3dPaulHarvey/Cycloidal-Robot-Wrist-3DOF-C.L.A.W.1-/SolidWorks/3D3-F-J6- Cycloidal A 56 5 1.5 14-1.SLDPRT

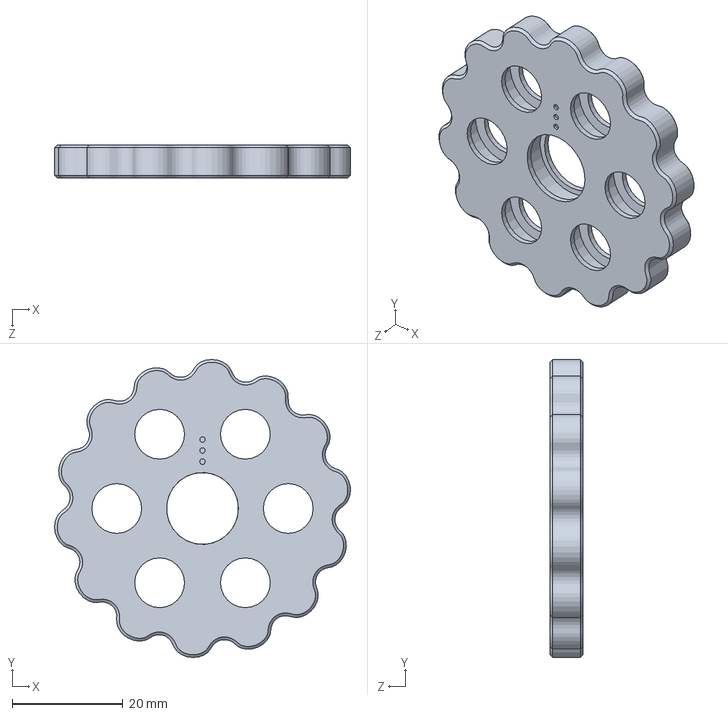
[picture p18: CAD file, 2022-01-06]
SolidWorks/3D3-F-J6- Cycloidal A 56 5 1.5 14-1.SLDPRT
53.5 x 53.9 x 6.00 mm
