3dPaulHarvey/Cycloidal-Robot-Wrist-3DOF-C.L.A.W.1-/SolidWorks/3D3- J6-3- 3MM PIN.SLDPRT

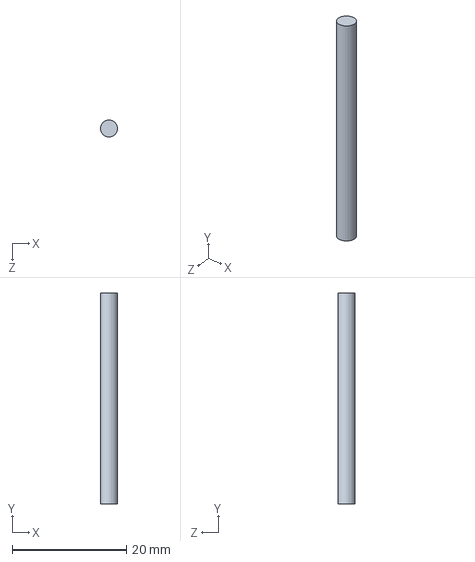
[picture p19: CAD file, 2022-01-06]
SolidWorks/3D3- J6-3- 3MM PIN.SLDPRT
3.00 x 37.0 x 3.00 mm
