3dPaulHarvey/Cycloidal-Robot-Wrist-3DOF-C.L.A.W.1-/SolidWorks/BEARING- 5x10x4.SLDPRT

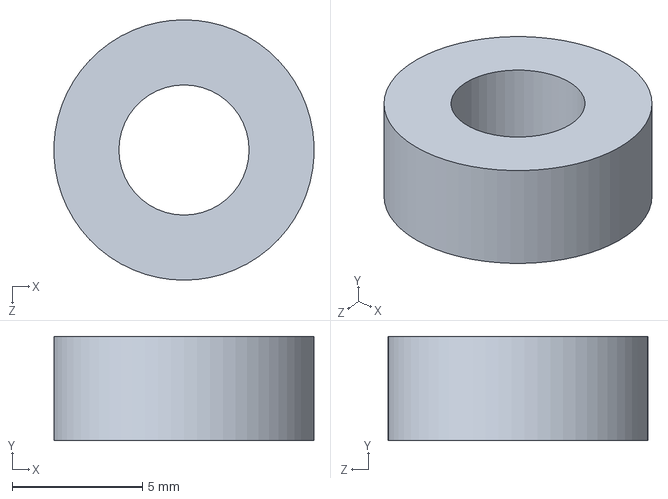
[picture p20: CAD file, 2022-01-06]
SolidWorks/BEARING- 5x10x4.SLDPRT
9.99 x 4.00 x 10.0 mm
