3dPaulHarvey/Cycloidal-Robot-Wrist-3DOF-C.L.A.W.1-/SolidWorks/3D3- J4 ECCENTRIC SHAFT.SLDPRT

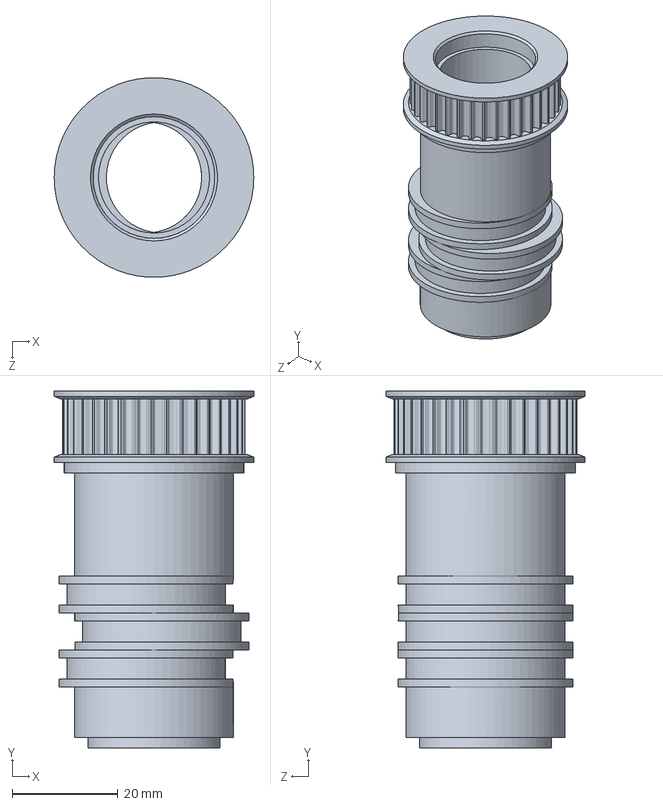
[picture p21: CAD file, 2022-01-06]
SolidWorks/3D3- J4 ECCENTRIC SHAFT.SLDPRT
37.7 x 67.5 x 37.7 mm
