3dPaulHarvey/Cycloidal-Robot-Wrist-3DOF-C.L.A.W.1-/SolidWorks/3D3-F-J5- 3MM PINS.SLDPRT

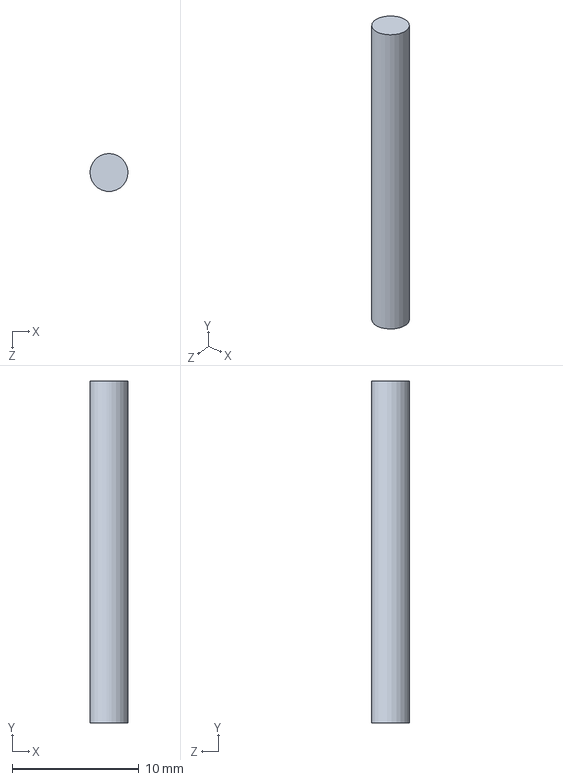
[picture p22: CAD file, 2022-01-06]
SolidWorks/3D3-F-J5- 3MM PINS.SLDPRT
2.99 x 27.0 x 3.00 mm
