3dPaulHarvey/Cycloidal-Robot-Wrist-3DOF-C.L.A.W.1-/SolidWorks/Cycloidal Lobes 19-1, 70, 5, 1.5- B.SLDPRT

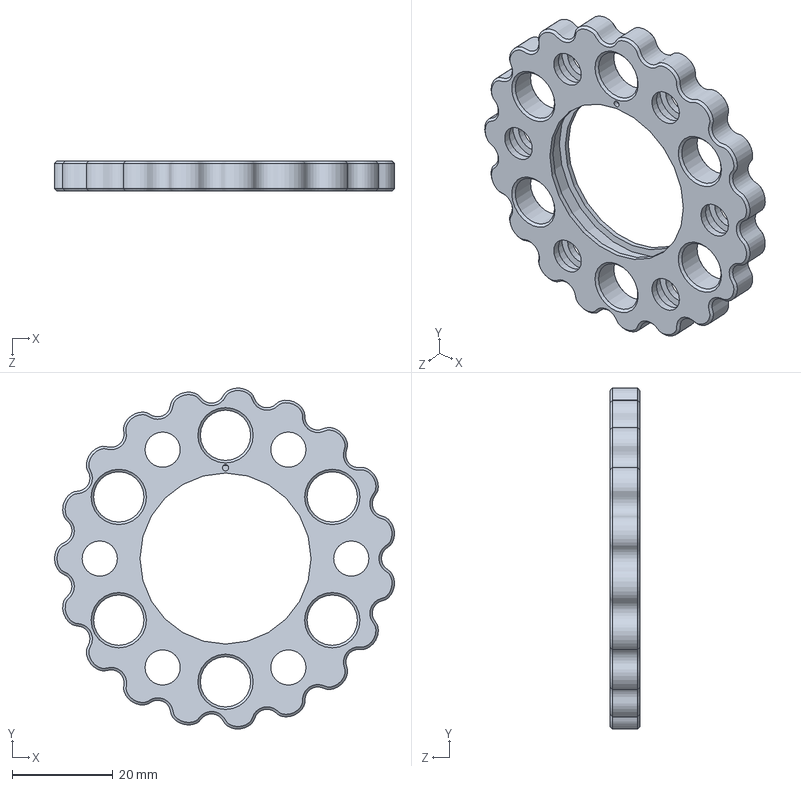
[picture p23: CAD file, 2022-01-06]
SolidWorks/Cycloidal Lobes 19-1, 70, 5, 1.5- B.SLDPRT
67.6 x 67.8 x 6.00 mm
