3dPaulHarvey/Cycloidal-Robot-Wrist-3DOF-C.L.A.W.1-/SolidWorks/BEARING- 3x5x5.SLDPRT

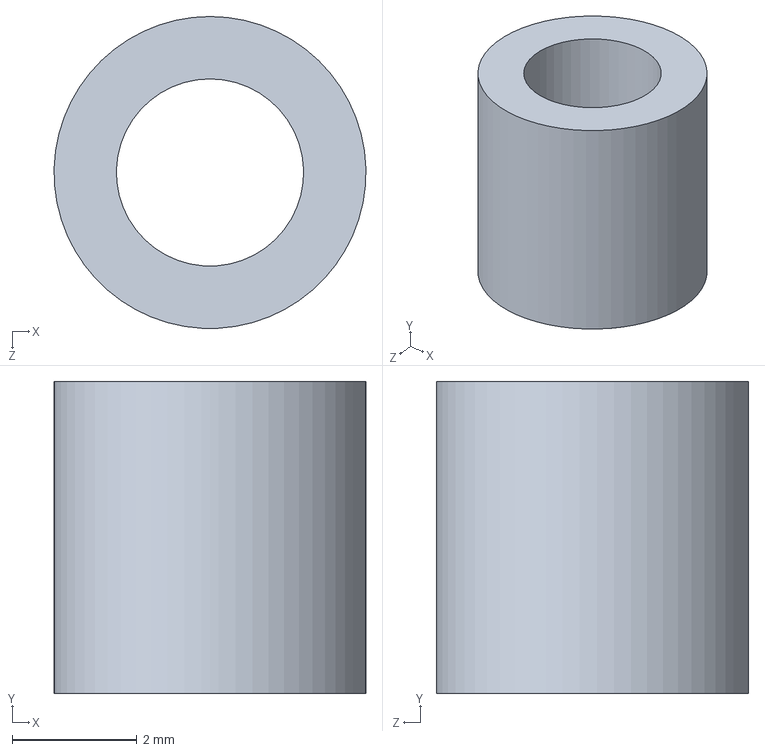
[picture p24: CAD file, 2022-01-06]
SolidWorks/BEARING- 3x5x5.SLDPRT
5.00 x 5.00 x 5.00 mm
