3dPaulHarvey/Cycloidal-Robot-Wrist-3DOF-C.L.A.W.1-/SolidWorks/3D3- J4- OUTPUT CARRIAGE.SLDPRT

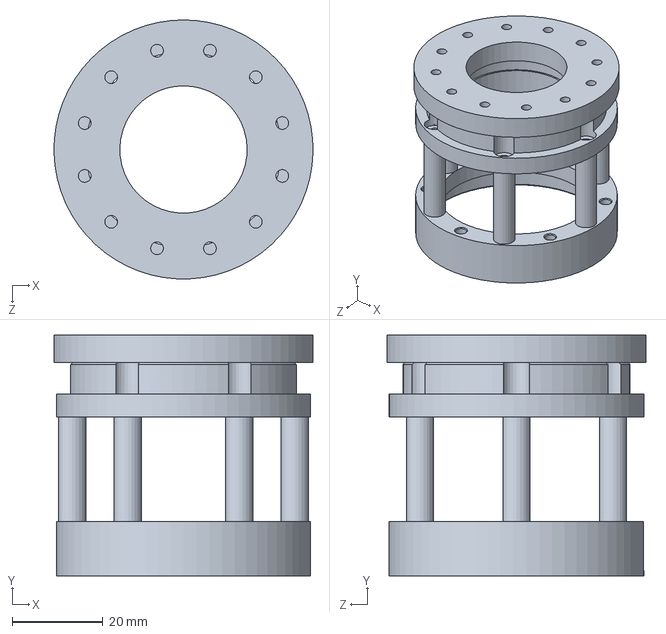
[picture p25: CAD file, 2022-01-06]
SolidWorks/3D3- J4- OUTPUT CARRIAGE.SLDPRT
57.0 x 53.0 x 57.0 mm
