3dPaulHarvey/Cycloidal-Robot-Wrist-3DOF-C.L.A.W.1-/SolidWorks/3D3- J5-2- MID WRIST FRAME.SLDPRT

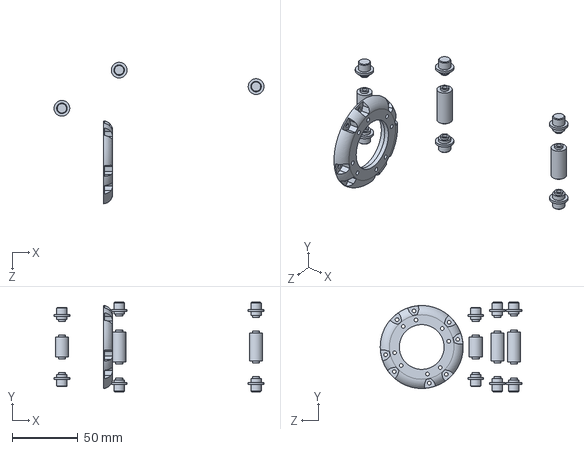
[picture p26: CAD file, 2022-01-06]
SolidWorks/3D3- J5-2- MID WRIST FRAME.SLDPRT
159.5 x 68.0 x 107.5 mm
