3dPaulHarvey/Cycloidal-Robot-Wrist-3DOF-C.L.A.W.1-/SolidWorks/3D3-J5-2- CYCLOIDAL 11-1rat 48dia 5dia 1.5ecc A.SLDPRT

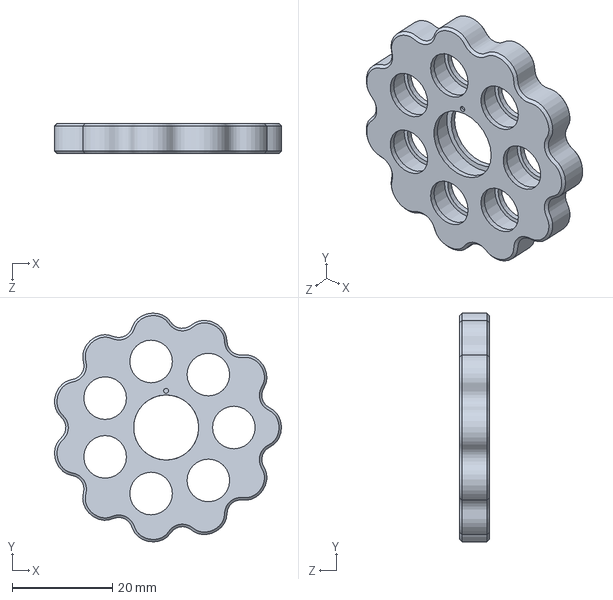
[picture p27: CAD file, 2022-01-06]
SolidWorks/3D3-J5-2- CYCLOIDAL 11-1rat 48dia 5dia 1.5ecc A.SLDPRT
45.3 x 45.6 x 6.00 mm
