3dPaulHarvey/Cycloidal-Robot-Wrist-3DOF-C.L.A.W.1-/SolidWorks/3D3-F-J5- DUMMY PINS.SLDPRT

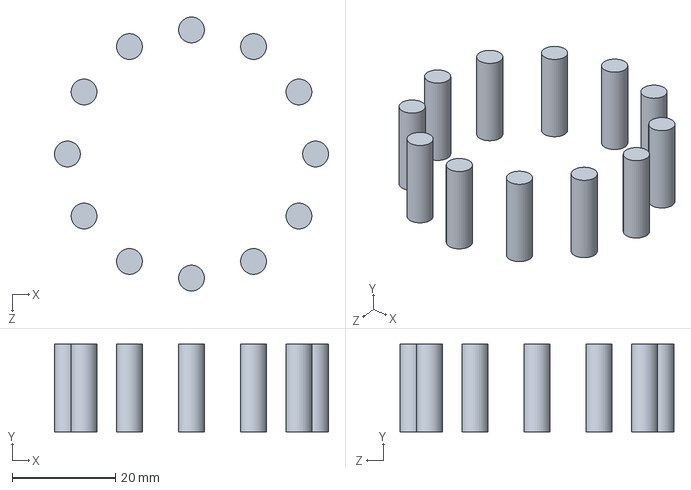
[picture p28: CAD file, 2022-01-06]
SolidWorks/3D3-F-J5- DUMMY PINS.SLDPRT
53.0 x 17.0 x 53.0 mm
