3dPaulHarvey/Cycloidal-Robot-Wrist-3DOF-C.L.A.W.1-/SolidWorks/3D3- J4- OUTER HOUSING.SLDPRT

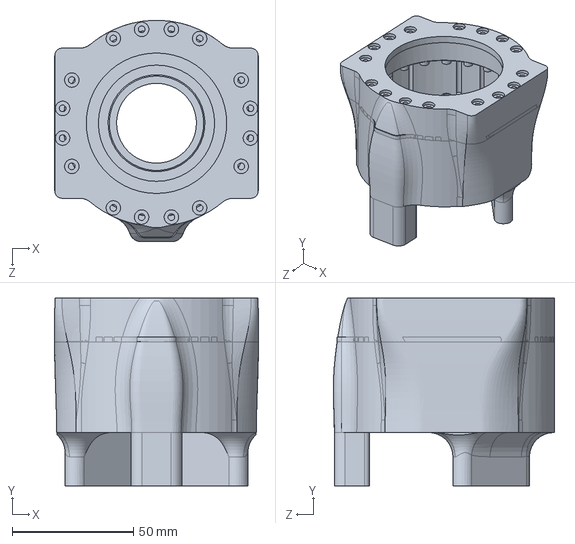
[picture p29: CAD file, 2022-01-06]
SolidWorks/3D3- J4- OUTER HOUSING.SLDPRT
84.2 x 77.5 x 91.4 mm
