3dPaulHarvey/Cycloidal-Robot-Wrist-3DOF-C.L.A.W.1-/SolidWorks/3D3- OUTER SHAFT.SLDPRT

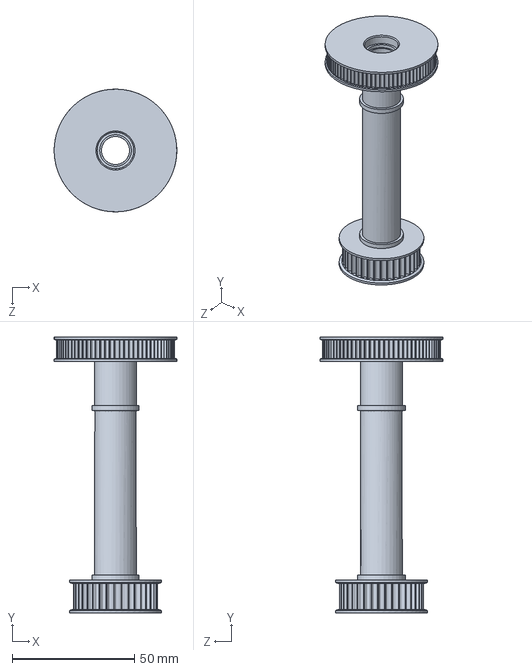
[picture p30: CAD file, 2022-01-06]
SolidWorks/3D3- OUTER SHAFT.SLDPRT
50.2 x 113.0 x 50.2 mm
