3dPaulHarvey/Cycloidal-Robot-Wrist-3DOF-C.L.A.W.1-/SolidWorks/3D3-F-J5- 3MM CORNER BAR B.SLDPRT

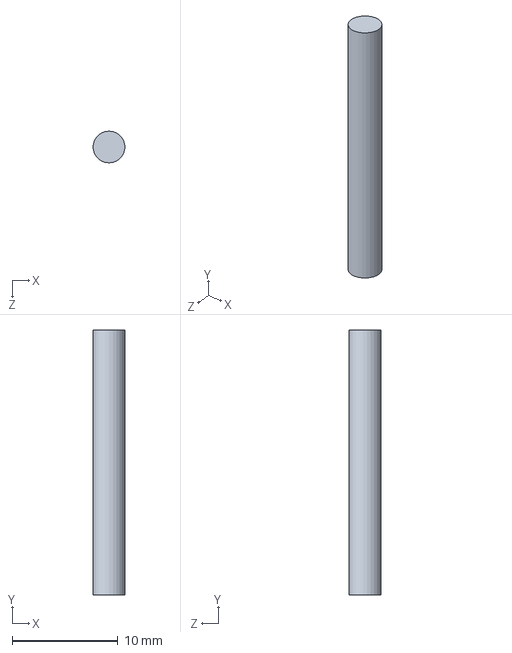
[picture p31: CAD file, 2022-01-06]
SolidWorks/3D3-F-J5- 3MM CORNER BAR B.SLDPRT
2.98 x 25.0 x 3.00 mm
