3dPaulHarvey/Cycloidal-Robot-Wrist-3DOF-C.L.A.W.1-/SolidWorks/gt2 35.SLDPRT

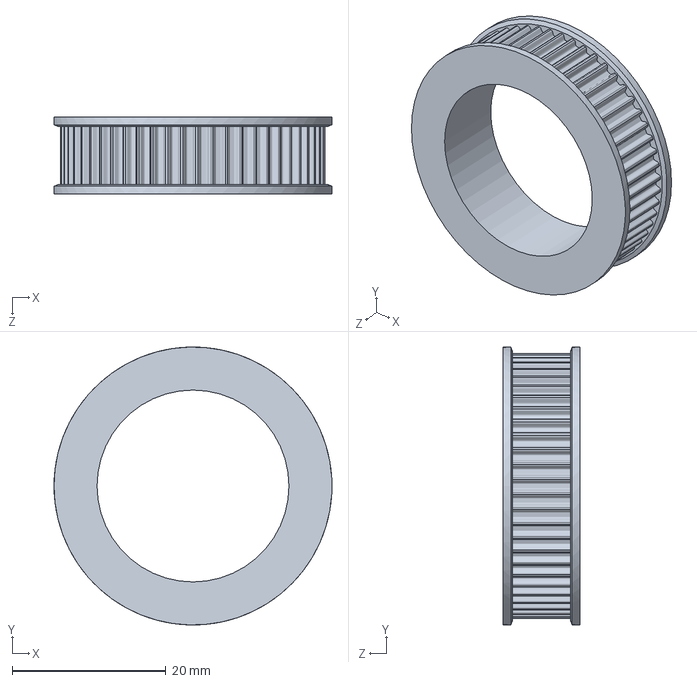
[picture p32: CAD file, 2022-01-02]
SolidWorks/gt2 35.SLDPRT
36.2 x 36.2 x 10.0 mm
