3dPaulHarvey/Cycloidal-Robot-Wrist-3DOF-C.L.A.W.1-/SolidWorks/44.SLDPRT

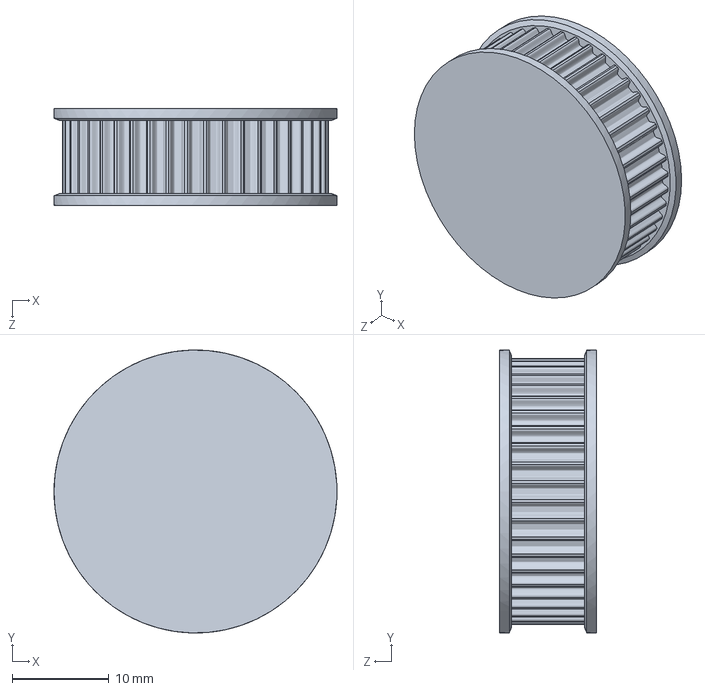
[picture p33: CAD file, 2022-01-02]
SolidWorks/44.SLDPRT
29.2 x 29.2 x 10.0 mm
