3dPaulHarvey/Cycloidal-Robot-Wrist-3DOF-C.L.A.W.1-/SolidWorks/3D3- J6-3- CORNER PULLEY.SLDPRT

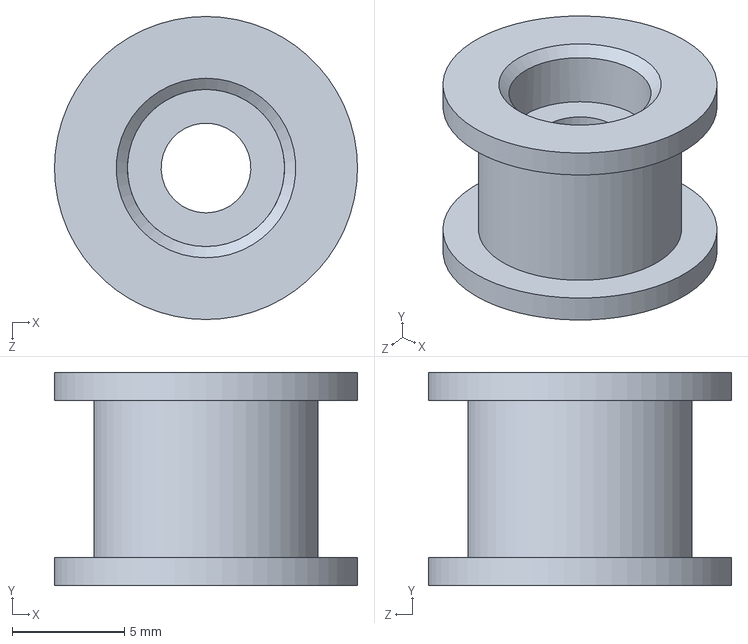
[picture p34: CAD file, 2022-01-02]
SolidWorks/3D3- J6-3- CORNER PULLEY.SLDPRT
13.5 x 9.50 x 13.5 mm
