3dPaulHarvey/Cycloidal-Robot-Wrist-3DOF-C.L.A.W.1-/SolidWorks/3D3- J6-3- 3MM BAR.SLDPRT

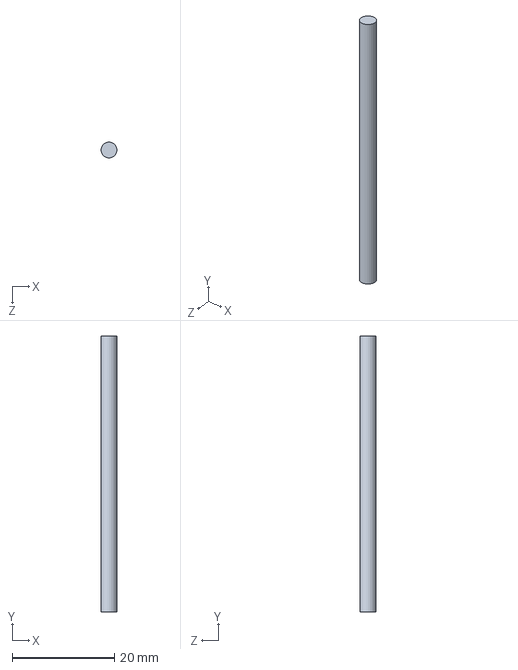
[picture p35: CAD file, 2022-01-02]
SolidWorks/3D3- J6-3- 3MM BAR.SLDPRT
3.10 x 54.0 x 3.10 mm
