3dPaulHarvey/Cycloidal-Robot-Wrist-3DOF-C.L.A.W.1-/SolidWorks/3D3- LEFT DRIVE PULLEY.SLDPRT

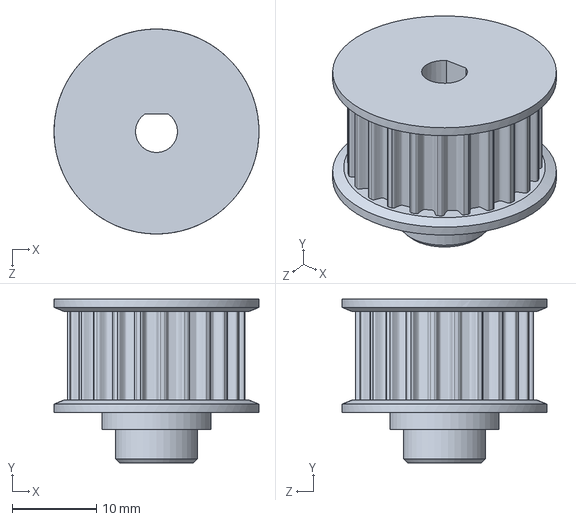
[picture p36: CAD file, 2022-01-02]
SolidWorks/3D3- LEFT DRIVE PULLEY.SLDPRT
24.4 x 19.5 x 24.4 mm
