3dPaulHarvey/Cycloidal-Robot-Wrist-3DOF-C.L.A.W.1-/SolidWorks/GT2-60T-ID 35.2-PD 38.2.SLDPRT

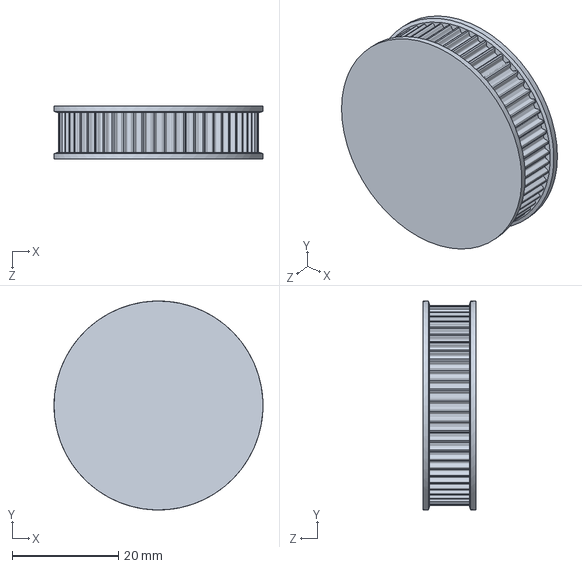
[picture p37: CAD file, 2022-01-02]
SolidWorks/GT2-60T-ID 35.2-PD 38.2.SLDPRT
39.4 x 39.4 x 10.0 mm
