3dPaulHarvey/Cycloidal-Robot-Wrist-3DOF-C.L.A.W.1-/SolidWorks/GT2-65T-ID 38.4-PD 41.4.SLDPRT

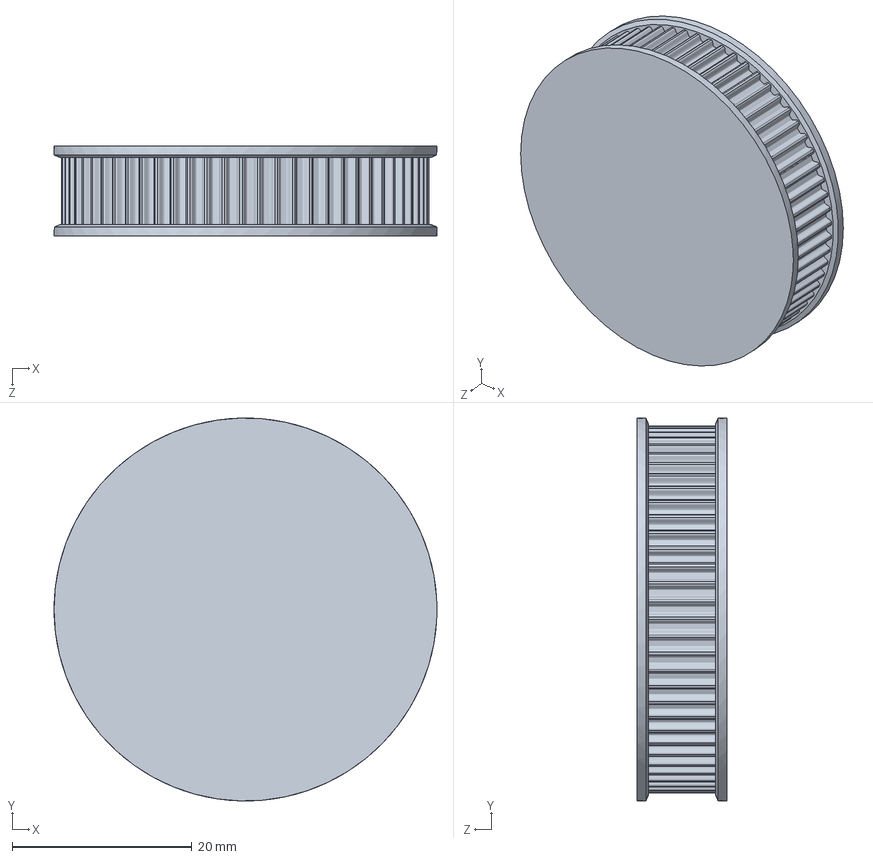
[picture p38: CAD file, 2022-01-02]
SolidWorks/GT2-65T-ID 38.4-PD 41.4.SLDPRT
42.6 x 42.6 x 10.0 mm
