3dPaulHarvey/Cycloidal-Robot-Wrist-3DOF-C.L.A.W.1-/SolidWorks/GT2-50T-ID 28.9-PD 31.85.SLDPRT

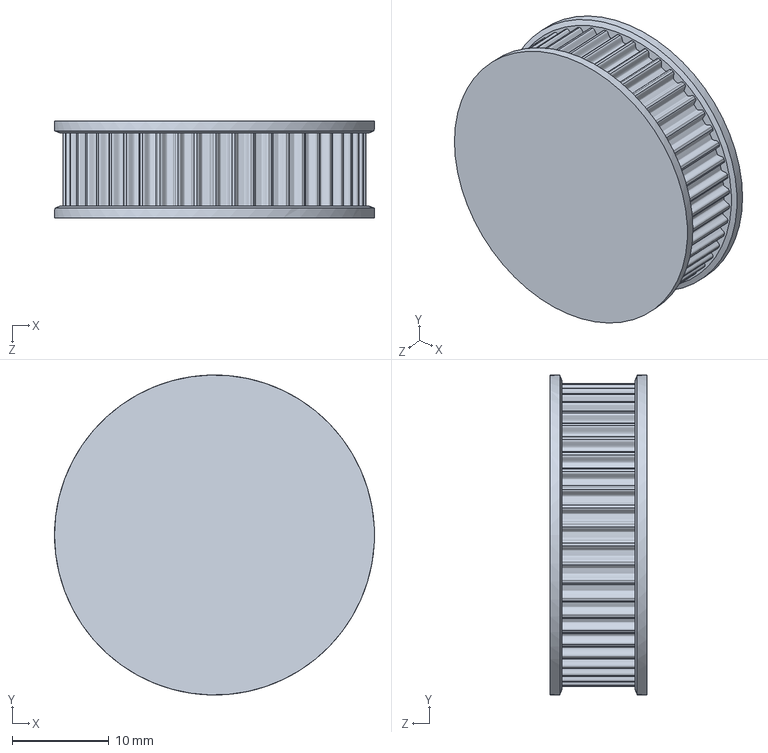
[picture p39: CAD file, 2022-01-02]
SolidWorks/GT2-50T-ID 28.9-PD 31.85.SLDPRT
33.0 x 33.0 x 10.0 mm
