3dPaulHarvey/Cycloidal-Robot-Wrist-3DOF-C.L.A.W.1-/SolidWorks/STEPPER 42 MM AZN2.SLDPRT

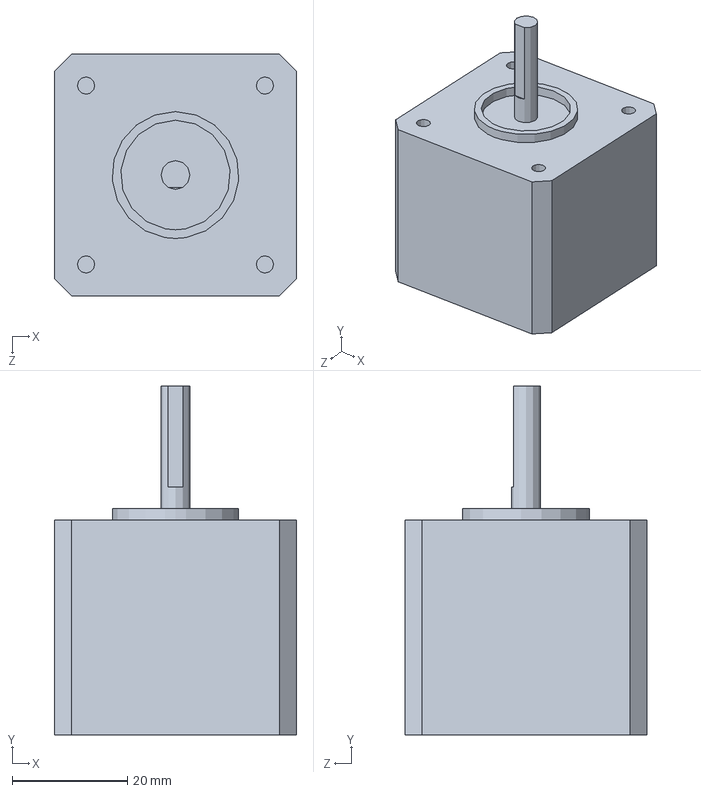
[picture p40: CAD file, 2022-01-02]
SolidWorks/STEPPER 42 MM AZN2.SLDPRT
42.0 x 60.5 x 42.0 mm
