3dPaulHarvey/Cycloidal-Robot-Wrist-3DOF-C.L.A.W.1-/SolidWorks/gt2 69.SLDPRT

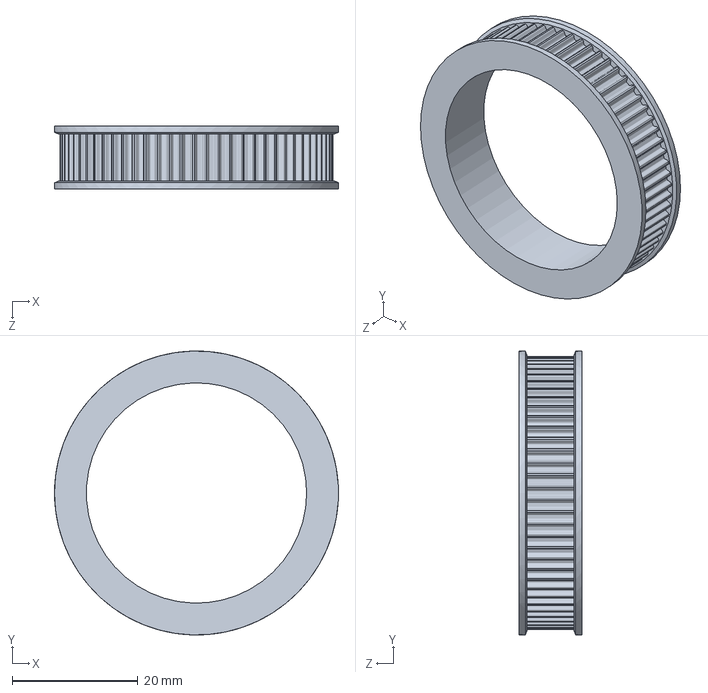
[picture p41: CAD file, 2022-01-02]
SolidWorks/gt2 69.SLDPRT
45.1 x 45.1 x 10.0 mm
