3dPaulHarvey/Cycloidal-Robot-Wrist-3DOF-C.L.A.W.1-/SolidWorks/GT2-72T-ID 42.9-PD 45.9.SLDPRT

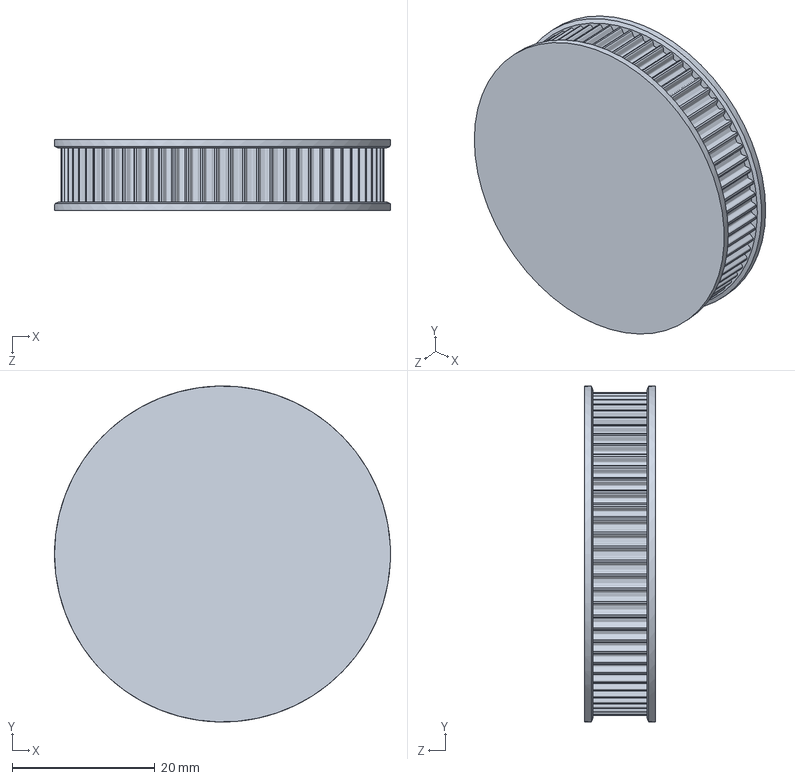
[picture p42: CAD file, 2022-01-02]
SolidWorks/GT2-72T-ID 42.9-PD 45.9.SLDPRT
47.0 x 47.0 x 10.0 mm
