3dPaulHarvey/Cycloidal-Robot-Wrist-3DOF-C.L.A.W.1-/SolidWorks/GT2-45T-ID 25.6-PD 28.2.SLDPRT

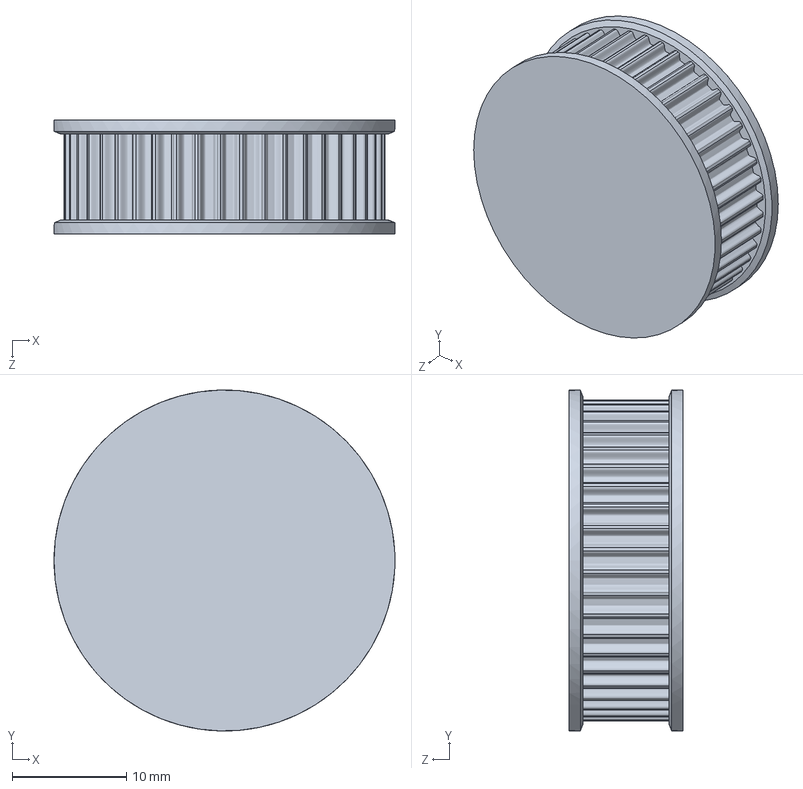
[picture p43: CAD file, 2022-01-02]
SolidWorks/GT2-45T-ID 25.6-PD 28.2.SLDPRT
29.9 x 29.8 x 10.0 mm
