3dPaulHarvey/Cycloidal-Robot-Wrist-3DOF-C.L.A.W.1-/SolidWorks/GT2-42T-ID 23.7-PD  26.7.SLDPRT

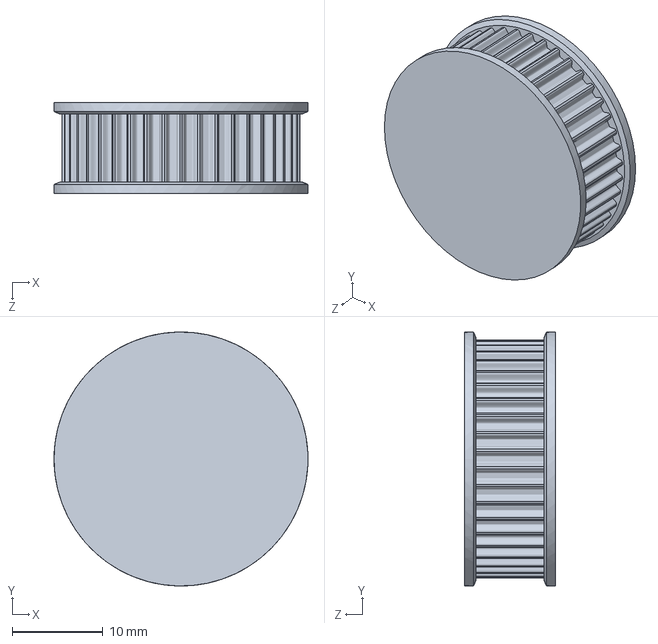
[picture p44: CAD file, 2022-01-02]
SolidWorks/GT2-42T-ID 23.7-PD 26.7.SLDPRT
27.9 x 27.9 x 10.0 mm
