3dPaulHarvey/Cycloidal-Robot-Wrist-3DOF-C.L.A.W.1-/SolidWorks/gt2 77.SLDPRT

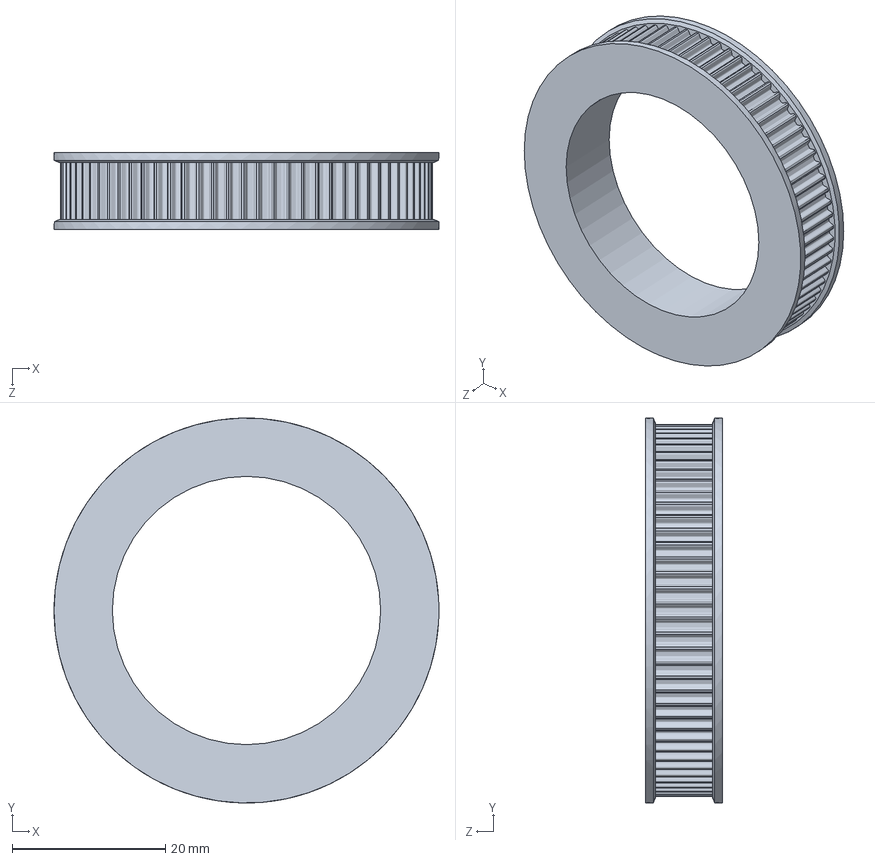
[picture p45: CAD file, 2022-01-02]
SolidWorks/gt2 77.SLDPRT
50.2 x 50.2 x 10.0 mm
