3dPaulHarvey/Cycloidal-Robot-Wrist-3DOF-C.L.A.W.1-/SolidWorks/BEARING- 6x10x3.SLDPRT

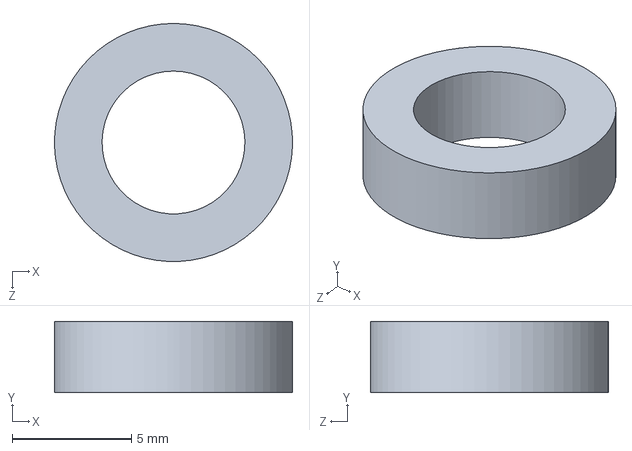
[picture p46: CAD file, 2022-01-02]
SolidWorks/BEARING- 6x10x3.SLDPRT
10.00 x 3.00 x 10.0 mm
