3dPaulHarvey/Cycloidal-Robot-Wrist-3DOF-C.L.A.W.1-/SolidWorks/GT2-48T-ID 27.6-PD 30.5.SLDPRT

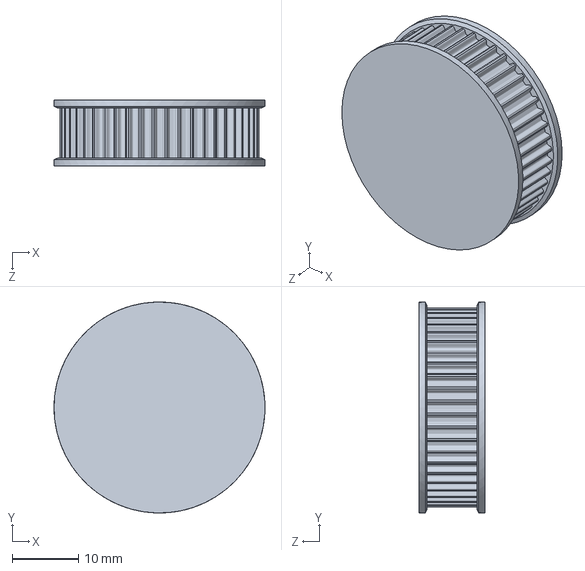
[picture p47: CAD file, 2022-01-02]
SolidWorks/GT2-48T-ID 27.6-PD 30.5.SLDPRT
31.8 x 31.8 x 10.0 mm
