3dPaulHarvey/Cycloidal-Robot-Wrist-3DOF-C.L.A.W.1-/SolidWorks/3D3- MOTOR ATTACH2.SLDPRT

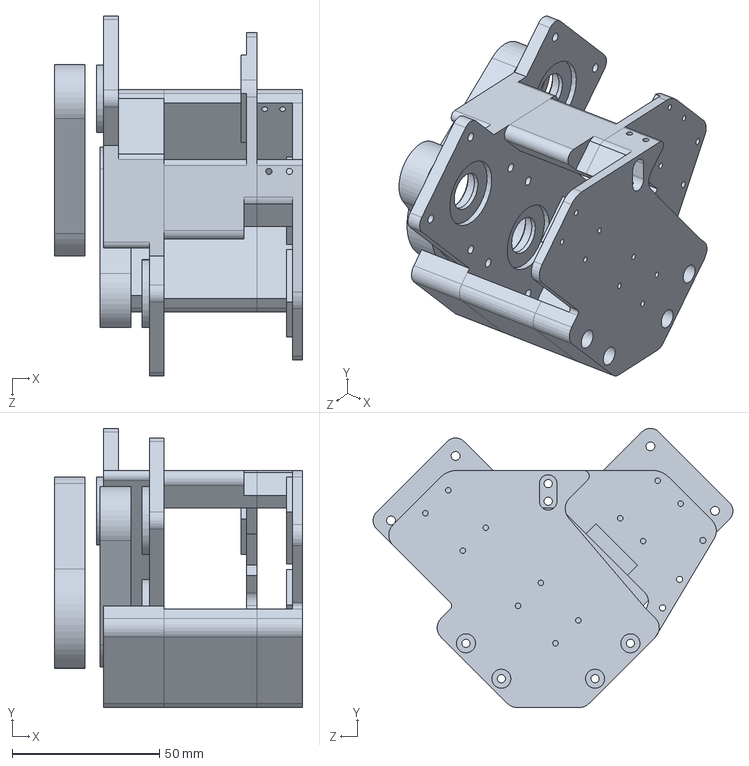
[picture p48: CAD file, 2022-01-02]
SolidWorks/3D3- MOTOR ATTACH2.SLDPRT
84.3 x 94.8 x 122.3 mm
